IbrahimEssamIbrahim/usbHub-microchip2514b/finalProduct/2.png

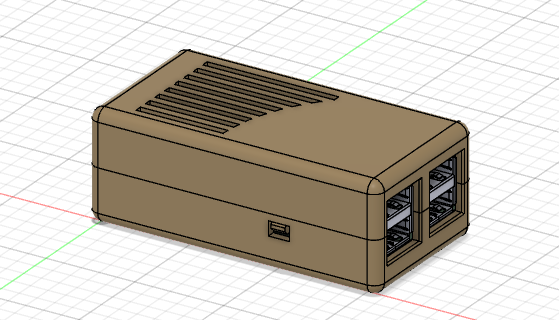
finalProduct/2.png
